Engjelli/ProyectoCapstoneFinal/Esquematico/Diagrama_esquematico_1.PNG

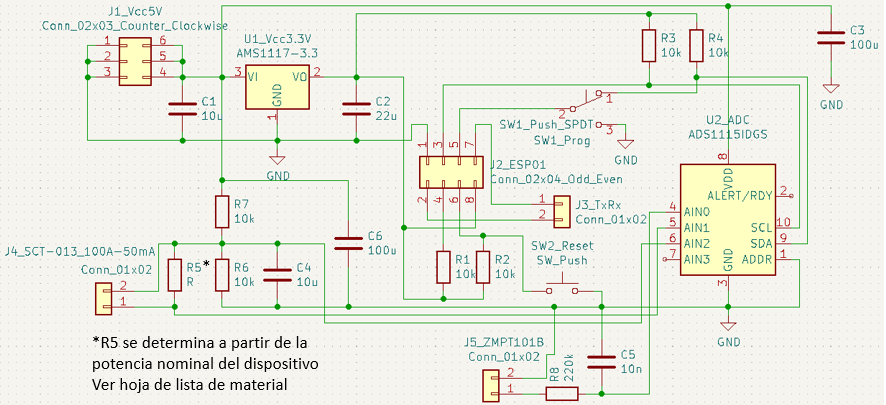
Esquematico/Diagrama_esquematico_1.PNG
