Engjelli/ProyectoCapstoneFinal/Imagenes/Diagramas/Descripcion_bloques_programa_ESP01.PNG

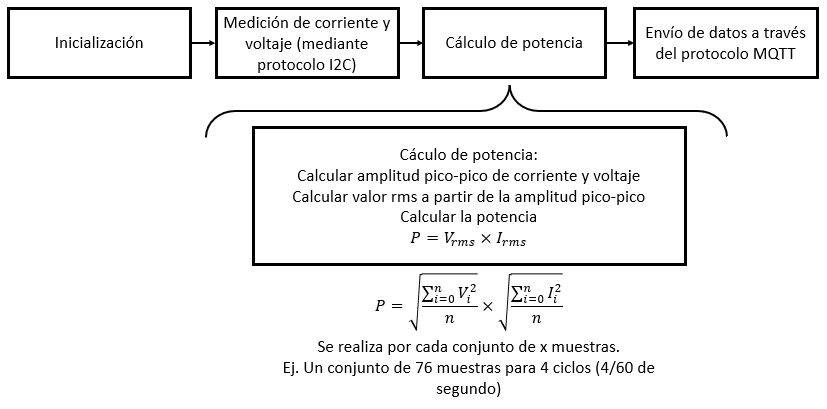
Imagenes/Diagramas/Descripcion_bloques_programa_ESP01.PNG
