Engjelli/ProyectoCapstoneFinal/Imagenes/Imagenes_circuitos/01_diagrama_sensor_corriente1.PNG

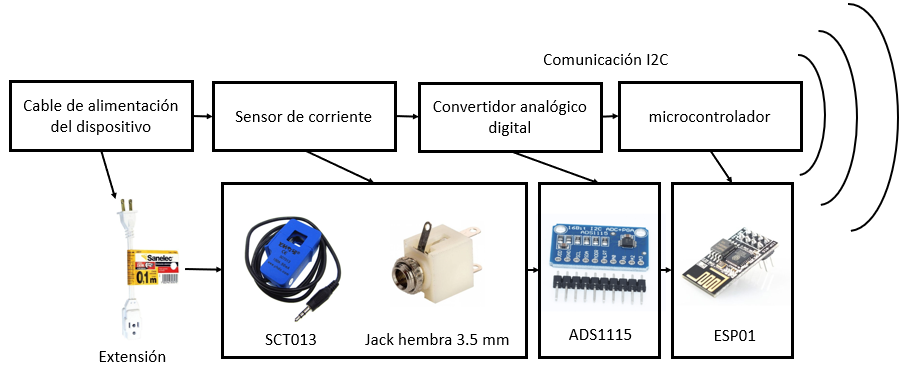
Imagenes/Imagenes_circuitos/01_diagrama_sensor_corriente1.PNG
