Engjelli/ProyectoCapstoneFinal/Imagenes/Imagenes_circuitos/02_diagrama_sensor_voltaje1.PNG

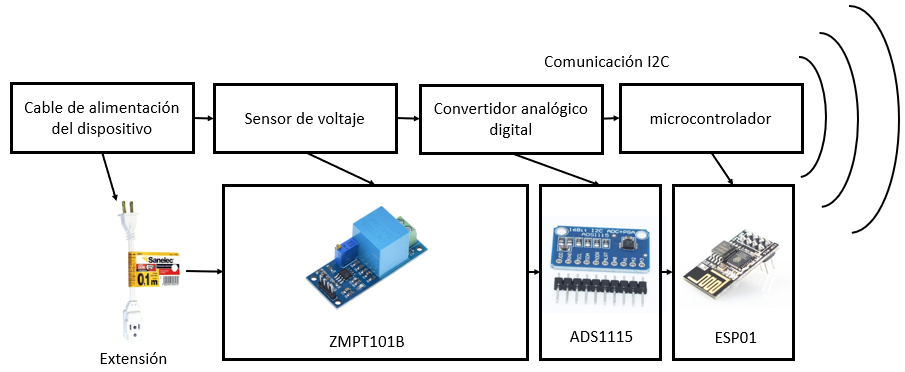
Imagenes/Imagenes_circuitos/02_diagrama_sensor_voltaje1.PNG
