Engjelli/ProyectoCapstoneFinal/Imagenes/Imagenes_prototipo/1645640526854.jpg

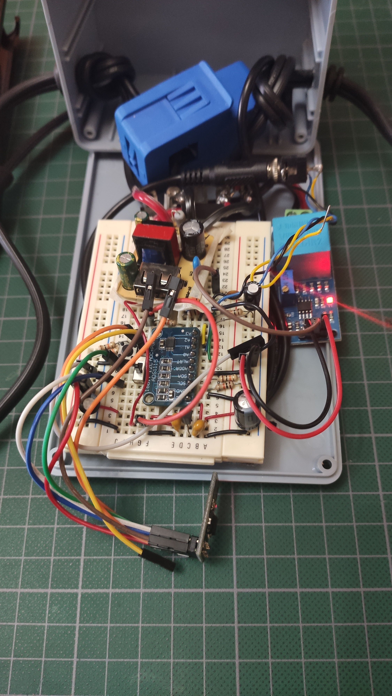
Imagenes/Imagenes_prototipo/1645640526854.jpg
