Engjelli/ProyectoCapstoneFinal/Esquematico/Proyecto.kicad_sch

## KiCad design Esquematico/Proyecto.kicad_sch (2022-02-24)

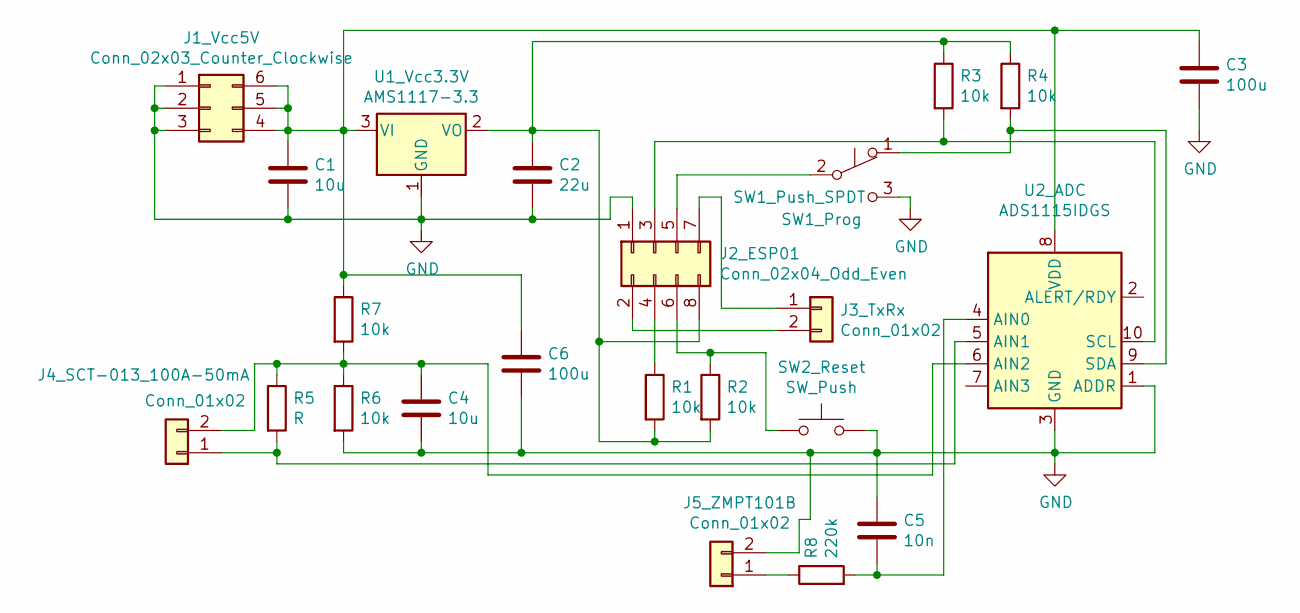
[picture p33: schematic Proyecto.kicad_sch]

Parts:
C1, C4: 10u
C2: 22u
C3, C6: 100u
C5: 10n
J1_Vcc5V: Conn_02x03_Counter_Clockwise
J2_ESP01: Conn_02x04_Odd_Even
J3_TxRx, J4_SCT-013_100A-50mA, J5_ZMPT101B: Conn_01x02
R1, R2, R3, R4, R6, R7: 10k
R5: R
R8: 220k
SW1_Prog: SW1_Push_SPDT
SW2_Reset: SW_Push
U1_Vcc3.3V: AMS1117-3.3; SOT-223-3_TabPin2
U2_ADC: ADS1115IDGS; TSSOP-10_3x3mm_P0.5mm

Connections:
unnamed: C1.1, C3.1, C6.1, J1_Vcc5V.4, J1_Vcc5V.5, J1_Vcc5V.6, R7.1, U1_Vcc3.3V.3 (VI), U2_ADC.8 (VDD)
unnamed: C1.2, C2.2, J1_Vcc5V.1, J1_Vcc5V.2, J1_Vcc5V.3, J2_ESP01.1, U1_Vcc3.3V.1 (GND)
unnamed: C2.1, J2_ESP01.8, R1.2, R2.2, R3.1, R4.1, U1_Vcc3.3V.2 (VO)
unnamed: C4.1, J4_SCT-013_100A-50mA.2, R5.1, R6.1, R7.2, U2_ADC.6 (AIN2)
unnamed: C4.2, C5.1, C6.2, J5_ZMPT101B.2, R6.2, SW2_Reset.2, U2_ADC.1 (ADDR), U2_ADC.3 (GND)
unnamed: C5.2, R8.2, U2_ADC.4 (AIN0)
unnamed: J2_ESP01.2, J3_TxRx.2
unnamed: J2_ESP01.3, R3.2, U2_ADC.10 (SCL)
unnamed: J2_ESP01.4, R1.1
unnamed: J2_ESP01.5, SW1_Prog.2 (B)
unnamed: J2_ESP01.6, R2.1, SW2_Reset.1
unnamed: J2_ESP01.7, J3_TxRx.1
unnamed: J4_SCT-013_100A-50mA.1, R5.2, U2_ADC.5 (AIN1)
unnamed: J5_ZMPT101B.1, R8.1
unnamed: R4.2, SW1_Prog.1 (A), U2_ADC.9 (SDA)
